NIKUNJMAHAJAN/Structural-Analysis-of-High-Pressure-PEM-Electrolyser-Using-FEA-Simulations/cad/1.JPG

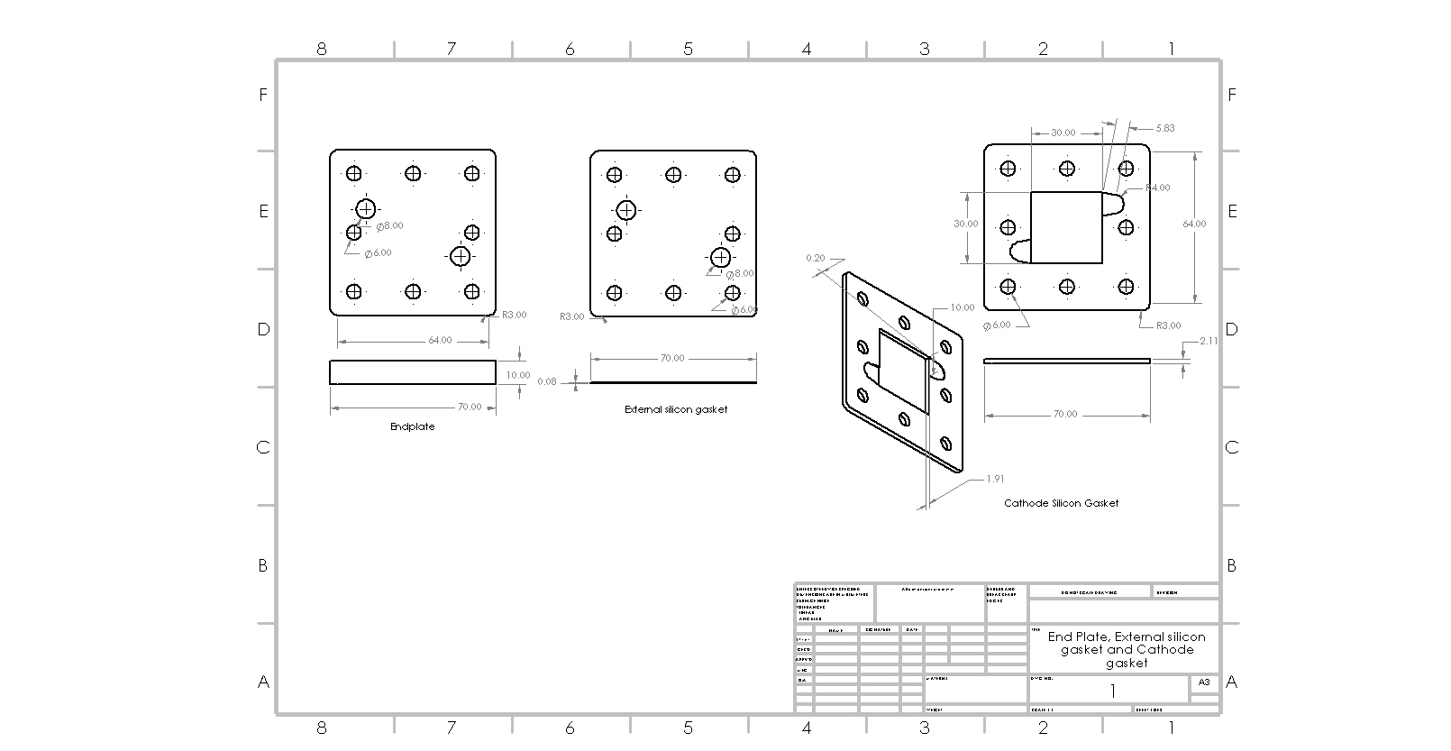
cad/1.JPG
