NIKUNJMAHAJAN/Structural-Analysis-of-High-Pressure-PEM-Electrolyser-Using-FEA-Simulations/cad/2.JPG

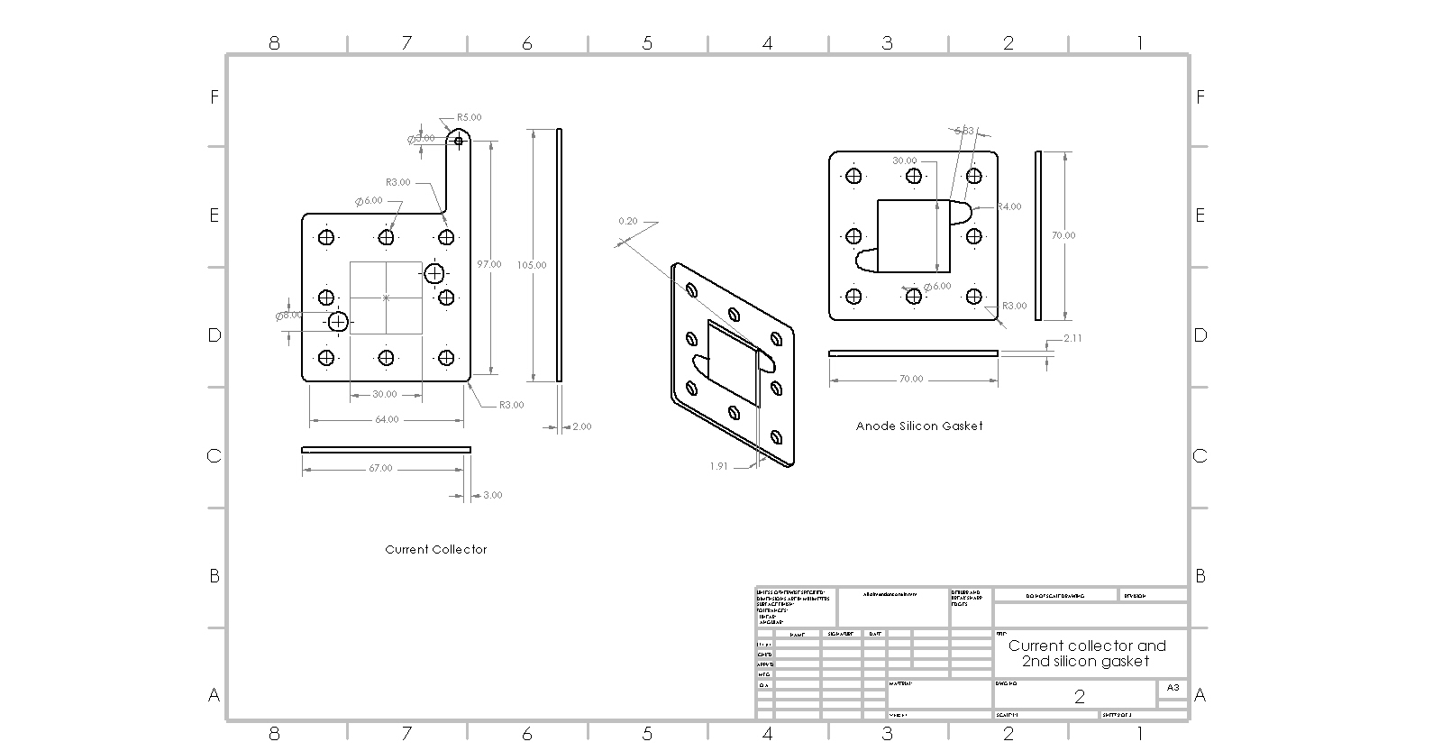
cad/2.JPG
