NIKUNJMAHAJAN/Structural-Analysis-of-High-Pressure-PEM-Electrolyser-Using-FEA-Simulations/cad/3.JPG

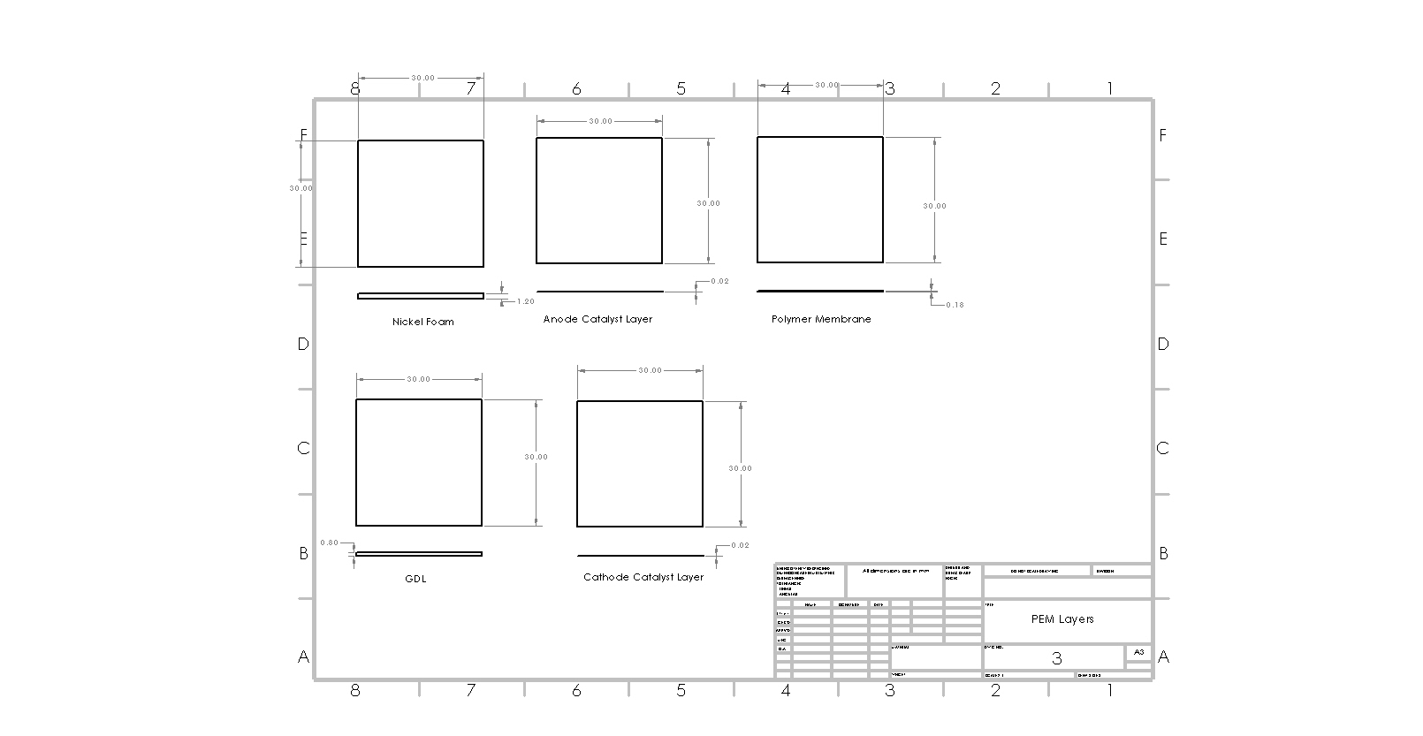
cad/3.JPG
